CheatingBoy6890/Open-Lasertag-System-Tagger/images/sr2fd1f407985aws3.png

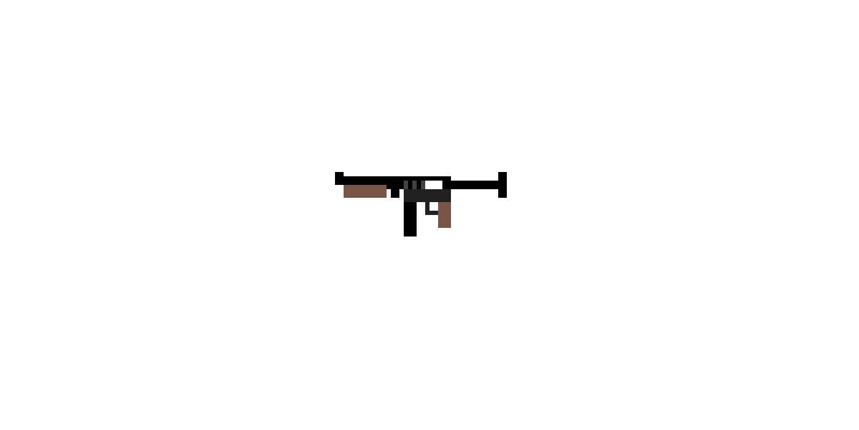
images/sr2fd1f407985aws3.png
