CheatingBoy6890/Open-Lasertag-System-Tagger/src/icons.h

#include "U8g2lib.h"
// #include <stdint.h>

// Uncomment one of these, you can actually use any of the supported Displays as long as their 128x64 pixels and using I2C

// SH1106 Display
U8G2_SH1106_128X64_NONAME_F_HW_I2C Display(U8G2_R1);
// SSD 1306 Display
// U8G2_SSD1306_128X64_NONAME_F_HW_I2C Display(U8G2_R1);

#define Cast_icon_width 15
#define Cast_icon_height 12

static uint8_t Cast_icon_bits[] PROGMEM = {
    0xfe, 0x3f, 0x03, 0x60, 0x03, 0x40, 0x00, 0x40, 0x00, 0x40, 0x02, 0x40,
    0x0e, 0x40, 0x18, 0x40, 0x33, 0x40, 0x66, 0x40, 0x6c, 0x72, 0x48,
    0x3e};

#define pistol_width 54
#define pistol_height 39

static uint8_t pistol_bits[] PROGMEM = {
    0xc0, 0xff, 0xff, 0xff, 0xff, 0xff, 0x3f, 0xc0, 0xff, 0xff, 0xff, 0xff,
    0xff, 0x3f, 0xc0, 0xf3, 0xff, 0x7f, 0xef, 0xfd, 0x3f, 0xc7, 0xfb, 0x00,
    0xfe, 0xde, 0xfb, 0x3f, 0xc7, 0xff, 0xff, 0xff, 0xff, 0xff, 0x3f, 0xc7,
    0xff, 0xff, 0xff, 0xff, 0xff, 0x3f, 0xf8, 0xff, 0xff, 0xff, 0xff, 0xff,
    0x00, 0xf8, 0xff, 0xff, 0xff, 0xff, 0xff, 0x00, 0xf8, 0xff, 0xff, 0xff,
    0xff, 0xff, 0x00, 0xc0, 0xff, 0xff, 0xff, 0xff, 0xff, 0x00, 0xc0, 0xff,
    0xff, 0xff, 0xff, 0xff, 0x00, 0xc0, 0xff, 0xff, 0xff, 0xff, 0xff, 0x00,
    0xc0, 0xff, 0x03, 0xff, 0xff, 0xff, 0x07, 0xc0, 0xff, 0x03, 0xff, 0xff,
    0xff, 0x07, 0xc0, 0xff, 0x03, 0xff, 0xff, 0x7f, 0x01, 0xc0, 0xff, 0x03,
    0xff, 0xff, 0xff, 0x00, 0xc0, 0xff, 0x03, 0xff, 0xff, 0xff, 0x07, 0xc0,
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
    0x00, 0x00, 0x00, 0x00, 0xe7, 0xef, 0x2f, 0xf7, 0x00, 0x00, 0x00, 0x00,
    0xf3, 0xf7, 0xef, 0xfb, 0x00, 0x00, 0x00, 0x00, 0xf1, 0xf7, 0x0f, 0x00,
    0x00, 0x00, 0x00, 0x00, 0xf8, 0xfb, 0x08, 0x00, 0x00, 0x00, 0x00,
    0x00};
